timborn/switched-bandpass-filter/docs/SOT89.png

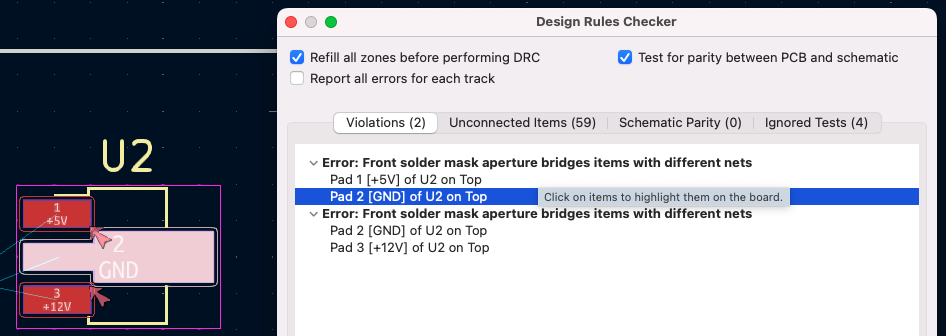
docs/SOT89.png
