timborn/switched-bandpass-filter/docs/v0.3 back.png

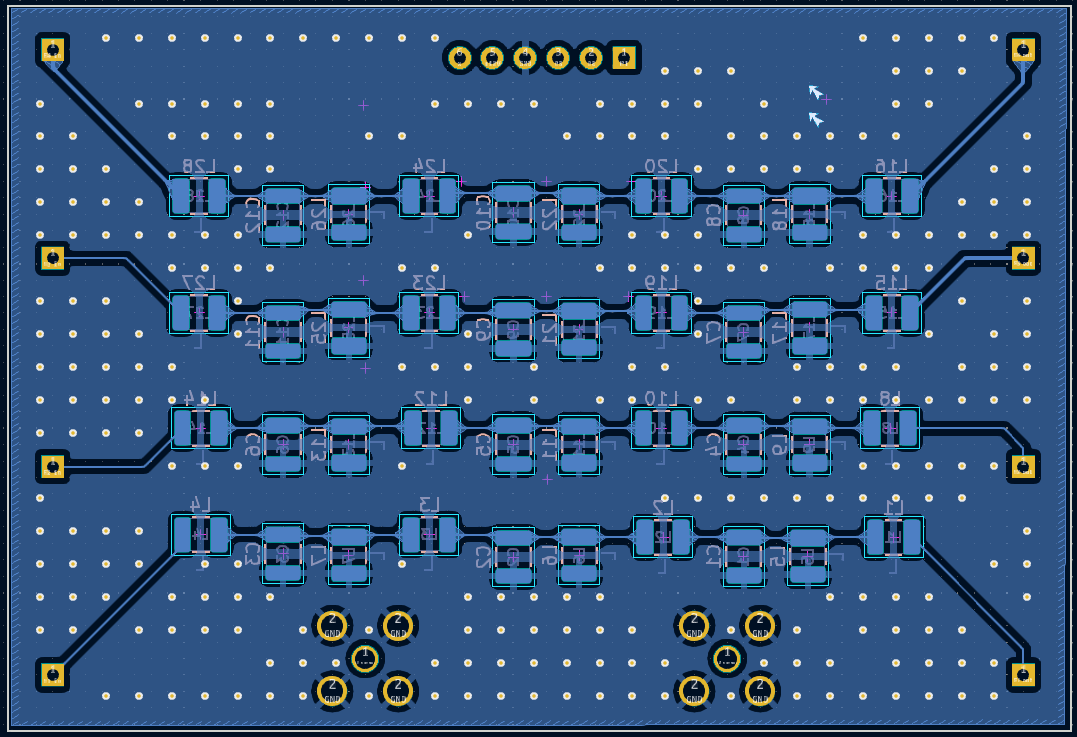
docs/v0.3 back.png
