timborn/switched-bandpass-filter/docs/v0.3 front.png

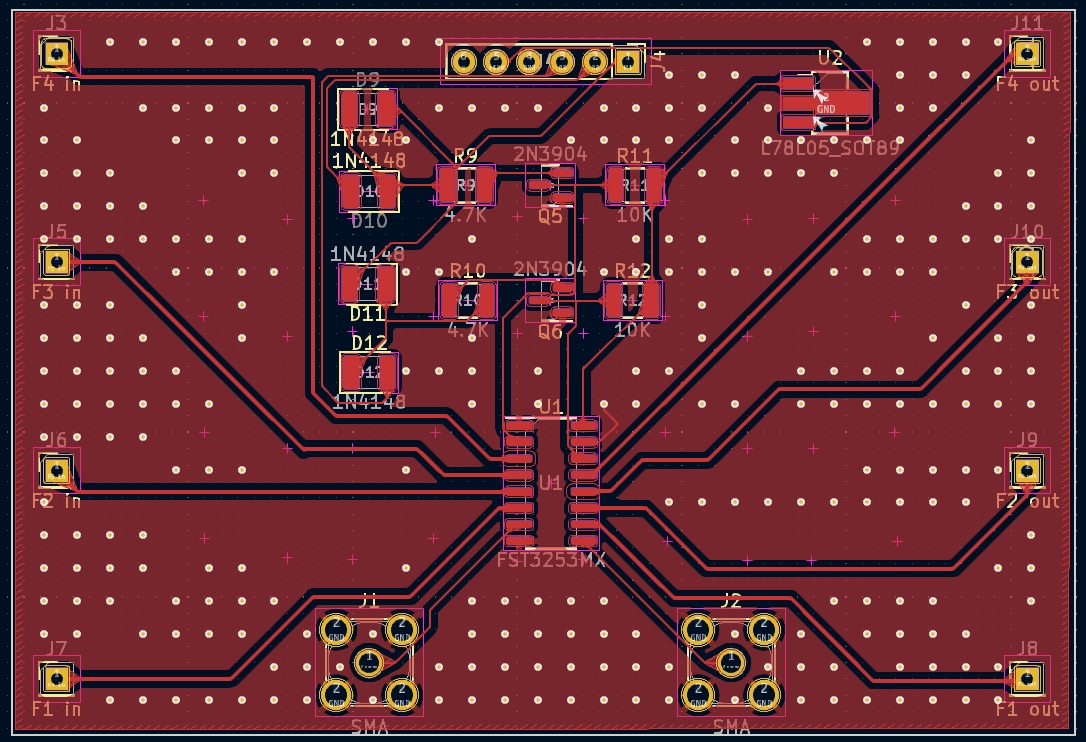
docs/v0.3 front.png
